DeVinci-Innovation-Center/BioWatch/images/BioWatch-Display.png

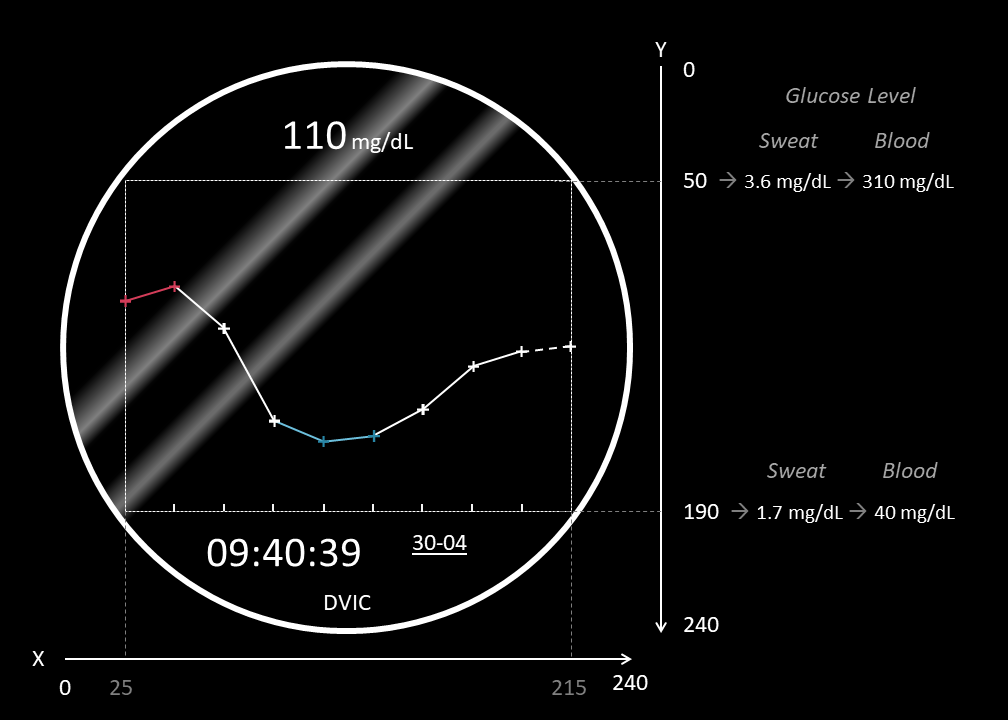
images/BioWatch-Display.png
