DeVinci-Innovation-Center/BioWatch/images/BioWatch_V2_Scheme.PNG

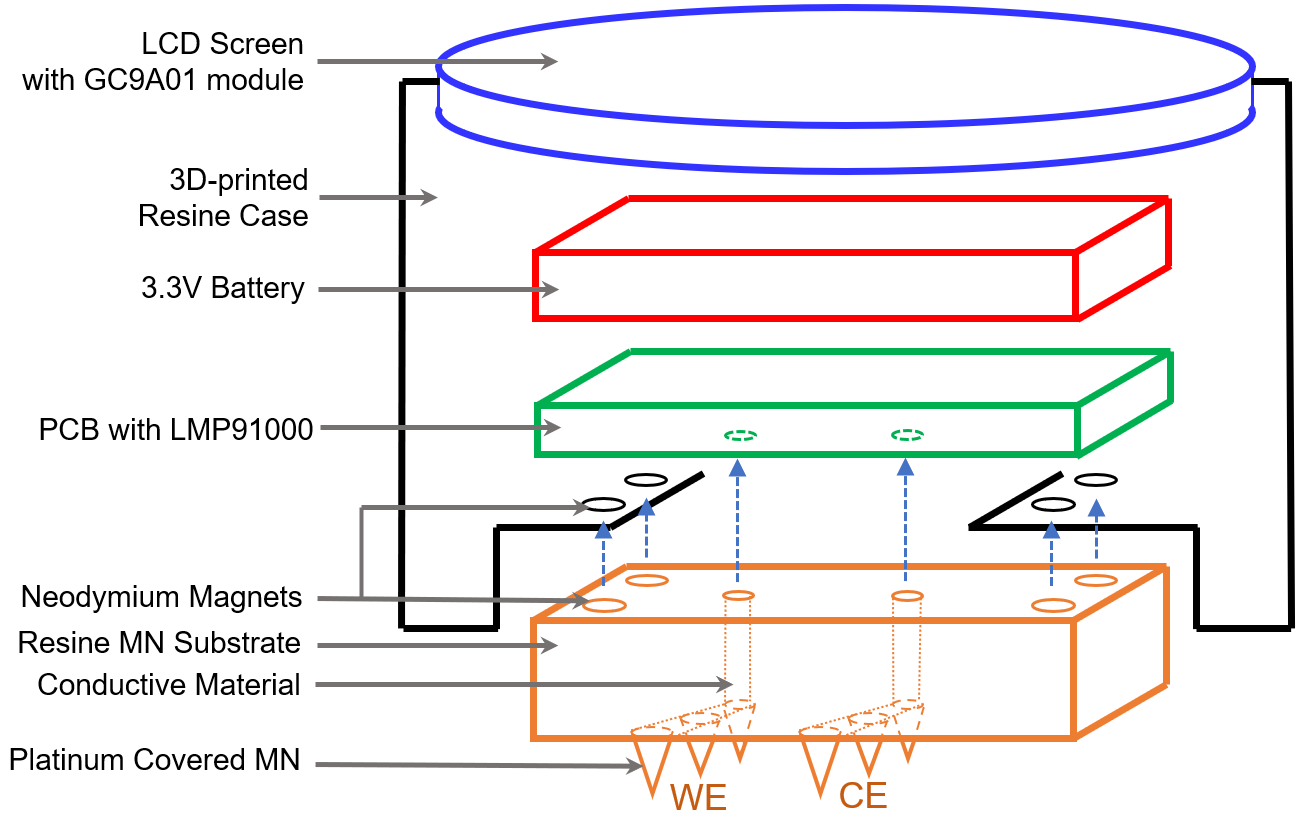
images/BioWatch_V2_Scheme.PNG
