DeVinci-Innovation-Center/BioWatch/images/functional_diagram.png

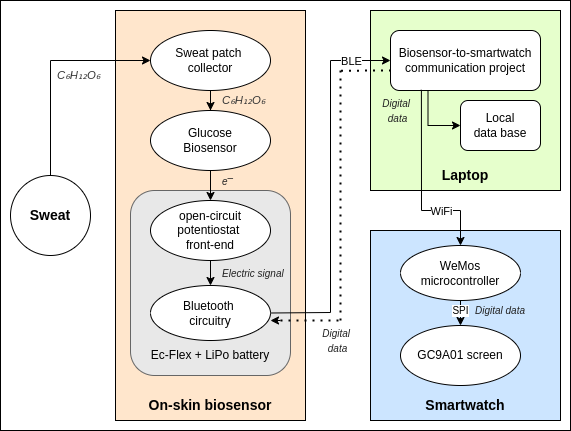
images/functional_diagram.png
