DeVinci-Innovation-Center/BioWatch/images/PCB-V2.png

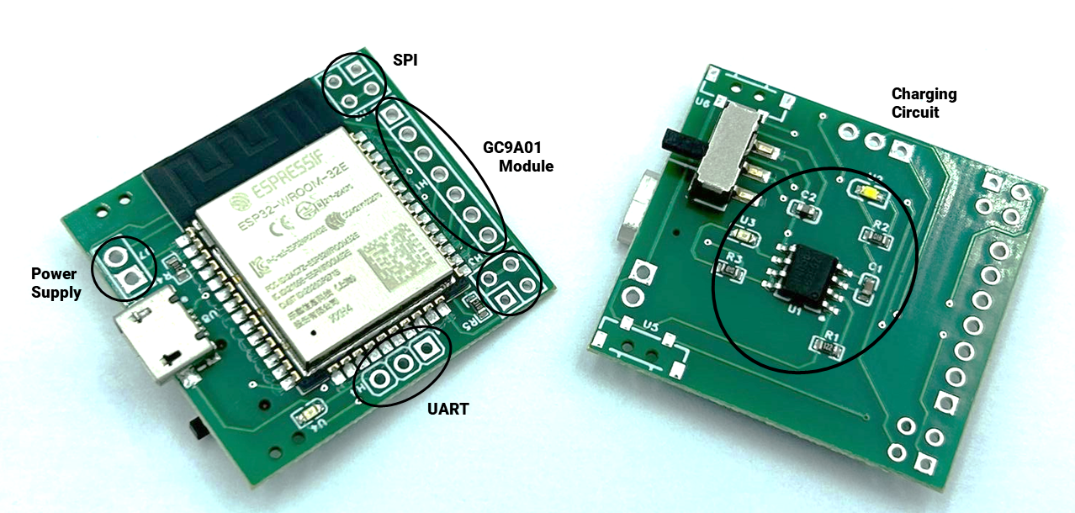
images/PCB-V2.png
