DeVinci-Innovation-Center/BioWatch/images/SmartWatch_V0.jpg

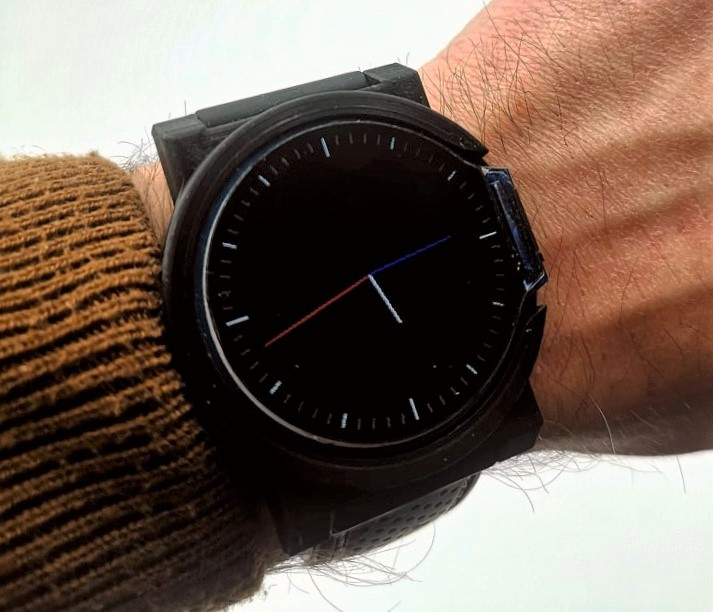
images/SmartWatch_V0.jpg
