DeVinci-Innovation-Center/BioWatch/images/Smartwatch_V0_black.png

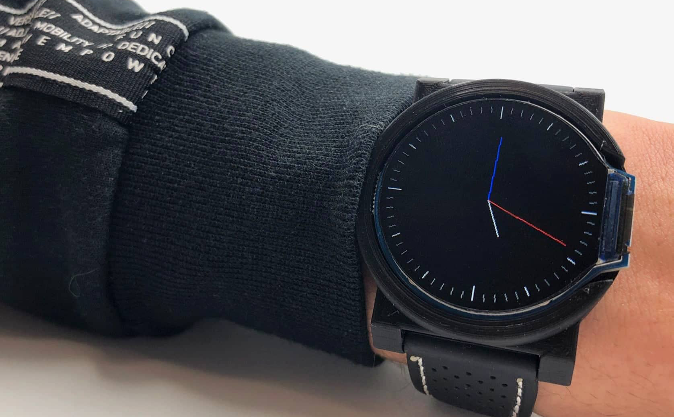
images/Smartwatch_V0_black.png
