DeVinci-Innovation-Center/BioWatch/images/sweat_collector_on_biosensor.jpg

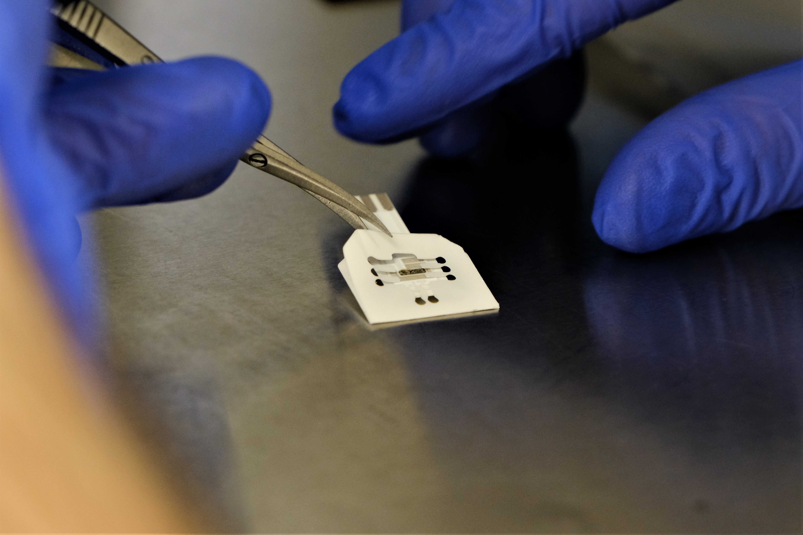
images/sweat_collector_on_biosensor.jpg
