DeVinci-Innovation-Center/BioWatch/software/ecflex-to-biowatch_wireless_communication/ecflex_server/Scheme ec-Flex.png

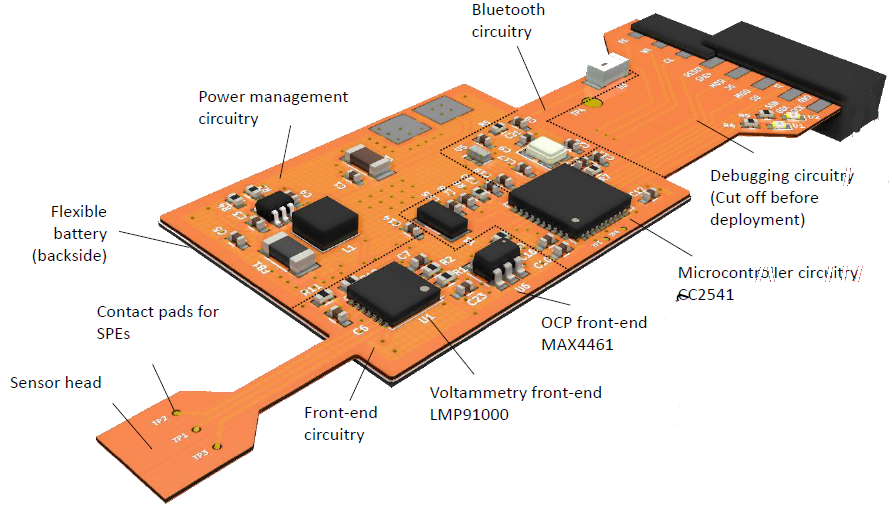
software/ecflex-to-biowatch_wireless_communication/ecflex_server/Scheme ec-Flex.png
