DeVinci-Innovation-Center/BioWatch/software/ecflex-to-biowatch_wireless_communication/ecflex_server/wearable_biosensing_system.jpg

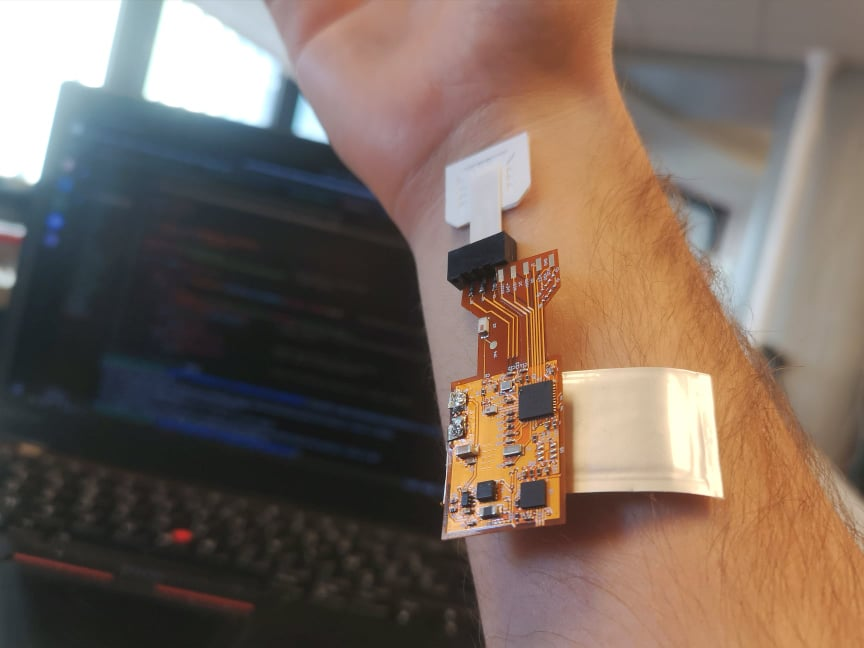
software/ecflex-to-biowatch_wireless_communication/ecflex_server/wearable_biosensing_system.jpg
