DeVinci-Innovation-Center/BioWatch/embedded_sensors/lmp91000/hardware/dev_board_texas_instruments/LMP91000_test-lactate_sensor.jpg

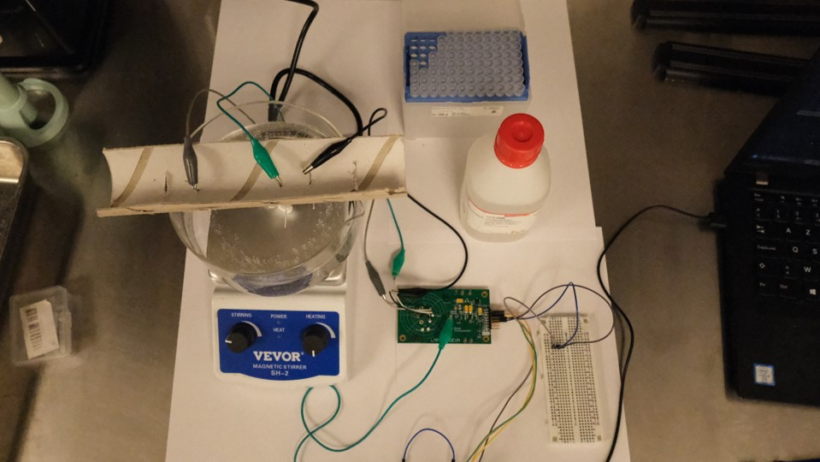
embedded_sensors/lmp91000/hardware/dev_board_texas_instruments/LMP91000_test-lactate_sensor.jpg
