DeVinci-Innovation-Center/BioWatch/images/128-lcd-module-measure.jpg

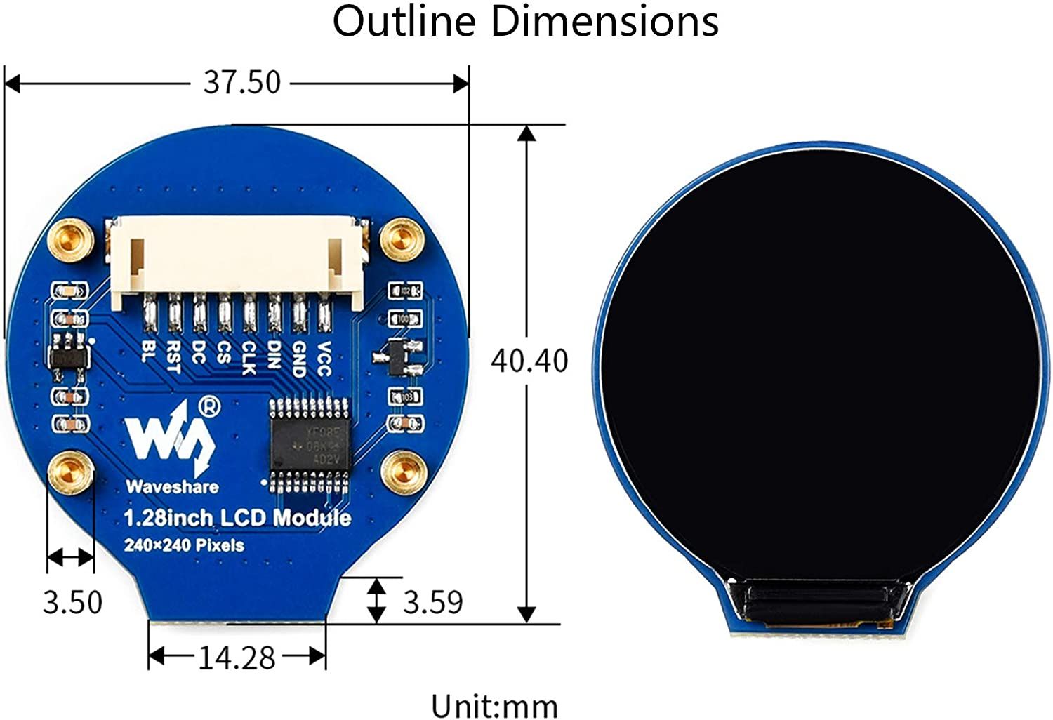
images/128-lcd-module-measure.jpg
