DeVinci-Innovation-Center/BioWatch/images/BioWatch-Characteristics.png

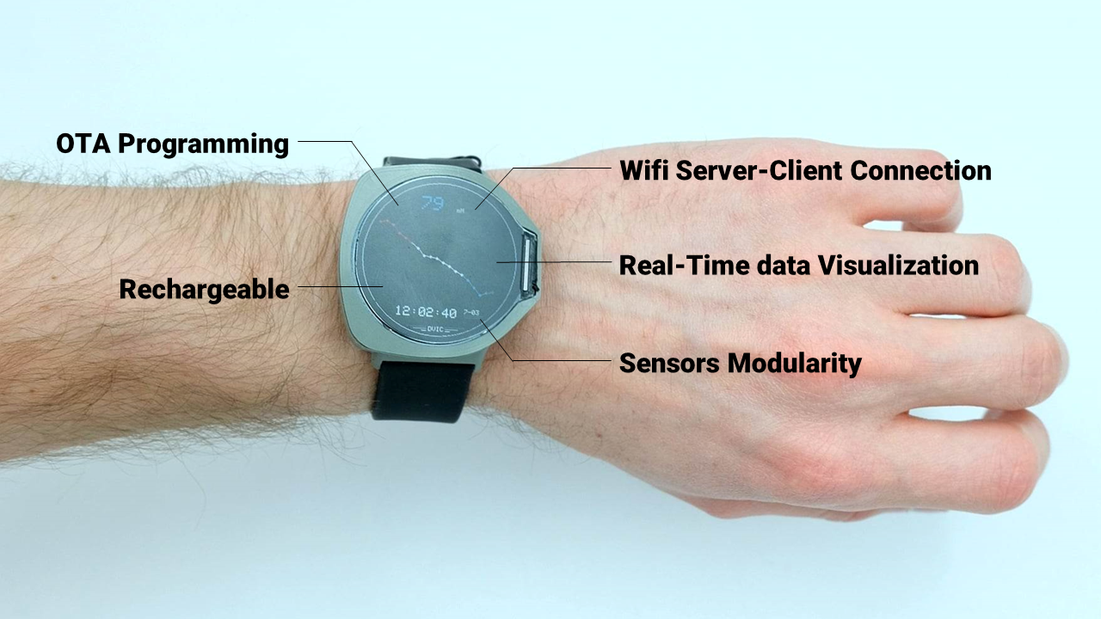
images/BioWatch-Characteristics.png
