DeVinci-Innovation-Center/BioWatch/images/LMP91000_test-lactate_sensor2.jpg

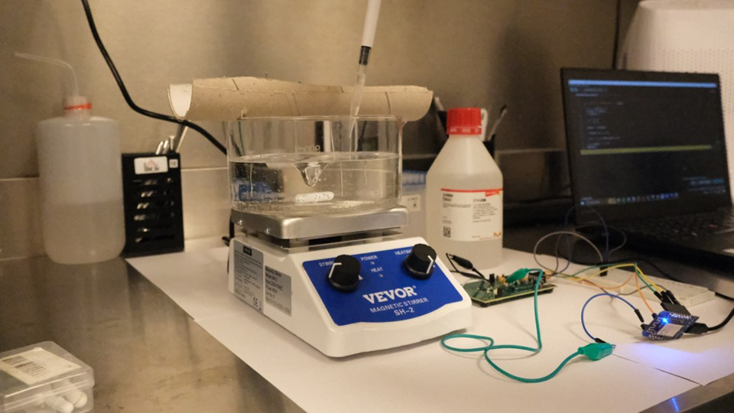
images/LMP91000_test-lactate_sensor2.jpg
