DeVinci-Innovation-Center/BioWatch/software/ecflex-to-biowatch_wireless_communication/biowatch_client/graphic_design/print_a_splash/print_a_splash.ino

#include "frames.h"

#include <SPI.h>
#include <TFT_eSPI.h> // Hardware-specific library
TFT_eSPI tft = TFT_eSPI();

void setup() {
  // put your setup code here, to run once:
tft.init();
  tft.setRotation(0);

  tft.setSwapBytes(true);
  tft.fillScreen(TFT_WHITE);
  
}

void loop() {
  // put your main code here, to run repeatedly:
for(int i=0; i<frames; i++)

{
  delay(40);
  tft.pushImage(60, 15, animation_width, animation_height, frame[i]);
  }

}
