DeVinci-Innovation-Center/BioWatch/software/ecflex-to-biowatch_wireless_communication/biowatch_client/graphic_design/print_graph_and_time/wifi-network.h

// WiFi Network SSID and password

#ifndef WIFI_NETWORK_H_  
#define WIFI_NETWORK_H_ 

// const char* myssid = "Livebox-E940";
// const char* mypassword = "ExFpUVKSKwjqYP4sbf";

const char* myssid = "PoleDeVinci_DVIC";
const char* mypassword = "8PfURsp!dvic";

#endif
