DeVinci-Innovation-Center/BioWatch/software/ecflex-to-biowatch_wireless_communication/biowatch_client/scan_wifi_networks/scan_wifi_networks.ino

/////////////////////////////////////////////////////////////////////
///      An Arduino script to scan WiFi networks availables       ///
/////////////////////////////////////////////////////////////////////

#include "ESP8266WiFi.h"   // .h file is the glossary of all functions from ESP8266WiFi library. 
WiFiClient client;

void setup() {
  Serial.begin(115200);
}

void loop() {
  Serial.println("Scan start");
  int n = WiFi.scanNetworks();            // WiFi.scanNetworks return the number of networks found
  Serial.println("Scan done");
  if (n==0) {
    Serial.println("No networks found");
  } else {
    Serial.print(n);
    Serial.println(" networks found");
    for (int i = 0; i < n; ++i) {         // Print SSID and RSSI (in dB) for each network found
      Serial.print(i + 1);  
      Serial.print(": "); 
      Serial.print(WiFi.SSID(i)); 
      Serial.print(" ("); 
      Serial.print(WiFi.RSSI(i)); 
      Serial.print(")");
      if (WiFi.encryptionType(i) == ENC_TYPE_NONE){     // Print a "*" if the WiFi Network is crypted 
        Serial.println(" ");                            
    } 
      else {
        Serial.println("*"); 
      }
     delay(10);
    }
  }
  Serial.println("");

  delay(5000);                   // Wait a bit befor scanning again
}
